maxim4ik163/ToneRealAdapter/Reference_PCB's/2 Mics_ An over-engineered solution – Exfil.co_files/IMG_7771.jpg

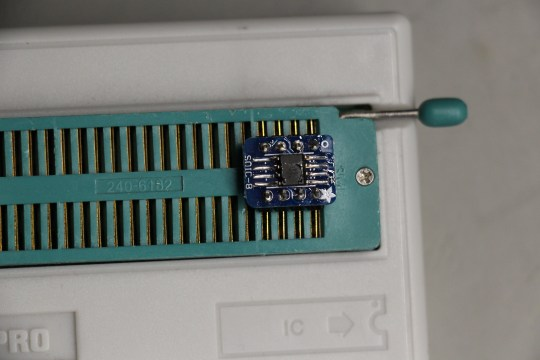
Reference_PCB's/2 Mics_ An over-engineered solution – Exfil.co_files/IMG_7771.jpg
