maxim4ik163/ToneRealAdapter/Reference_PCB's/2 Mics_ An over-engineered solution – Exfil.co_files/Screen-Shot-2018-05-16-11.10.27-AM.png

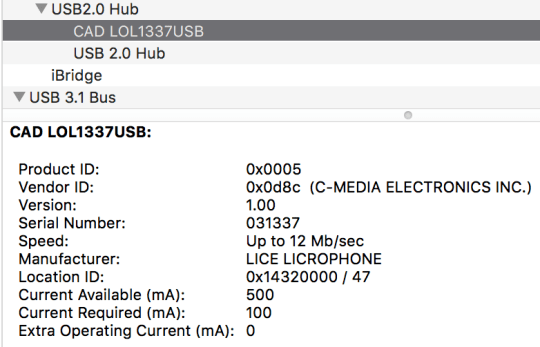
Reference_PCB's/2 Mics_ An over-engineered solution – Exfil.co_files/Screen-Shot-2018-05-16-11.10.27-AM.png
