maxim4ik163/ToneRealAdapter/Reference_PCB's/Bird UM-1_0.jpg

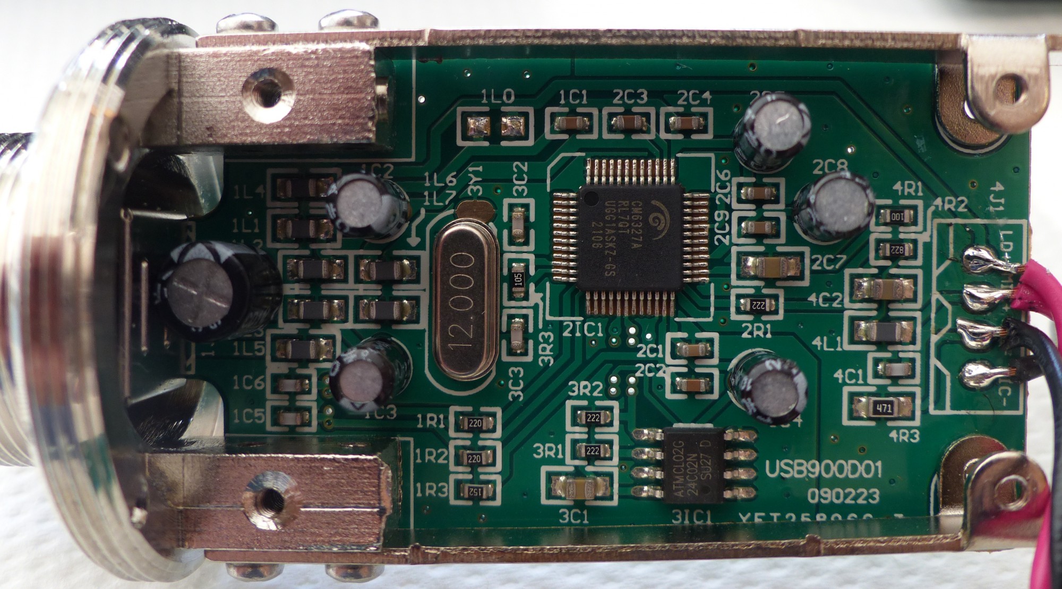
Reference_PCB's/Bird UM-1_0.jpg
