maxim4ik163/ToneRealAdapter/Reference_PCB's/blue_snowball_ice_1.0.jpg

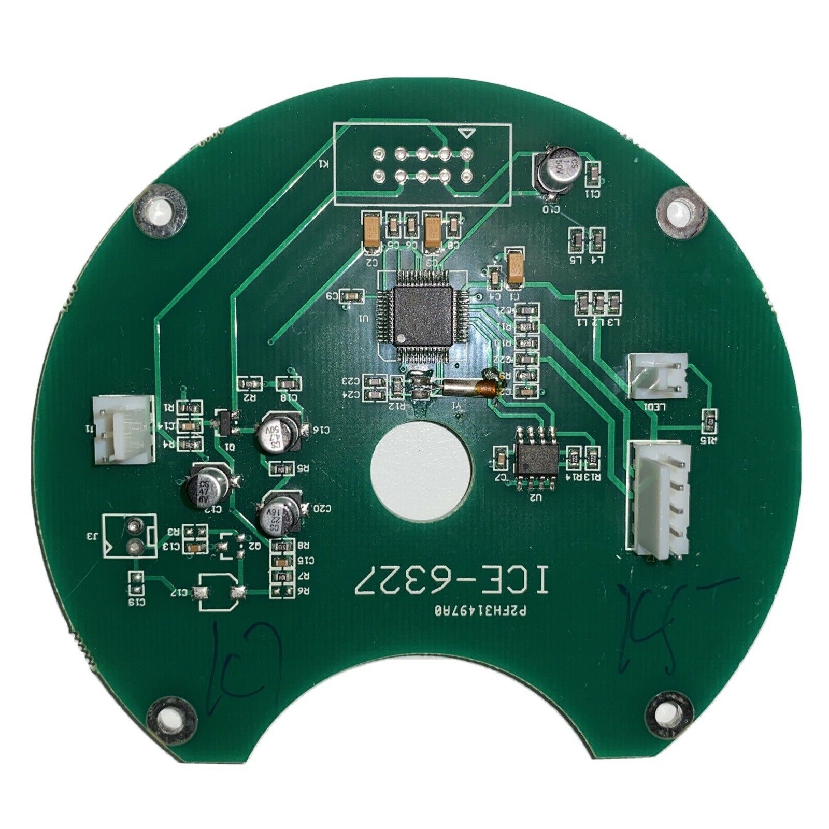
Reference_PCB's/blue_snowball_ice_1.0.jpg
