maxim4ik163/ToneRealAdapter/Reference_PCB's/blue_snowball_ice_1.1_back+mirror.png

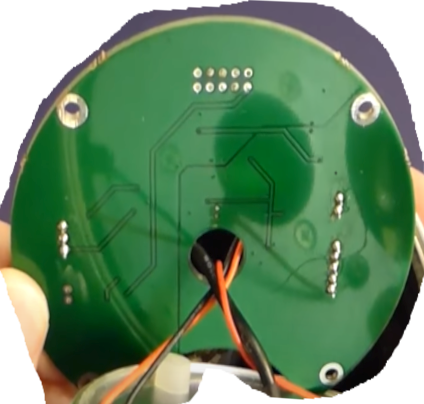
Reference_PCB's/blue_snowball_ice_1.1_back+mirror.png
