maxim4ik163/ToneRealAdapter/Reference_PCB's/blue_snowball_ice_1.2_back.png

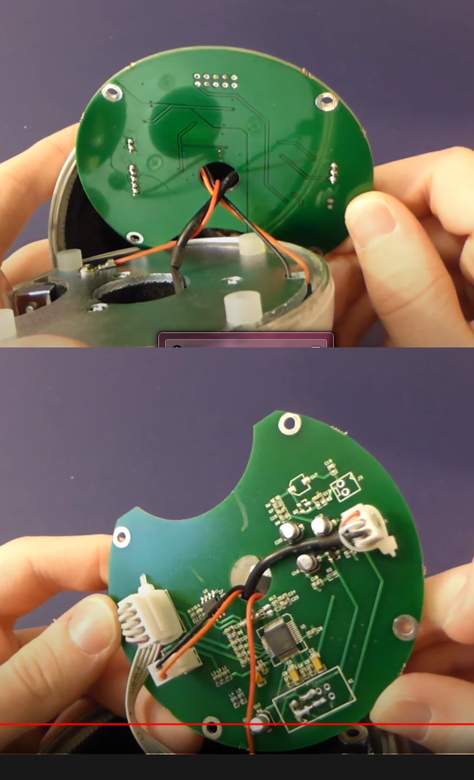
Reference_PCB's/blue_snowball_ice_1.2_back.png
