maxim4ik163/ToneRealAdapter/Reference_PCB's/blue_snowball_ice_1.3_back_mirror.png

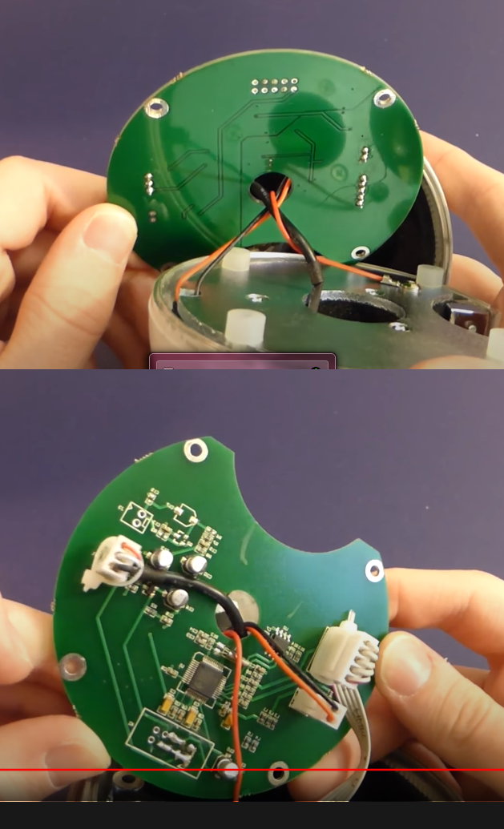
Reference_PCB's/blue_snowball_ice_1.3_back_mirror.png
