maxim4ik163/ToneRealAdapter/Reference_PCB's/blue_snowball_ice_1.4.png

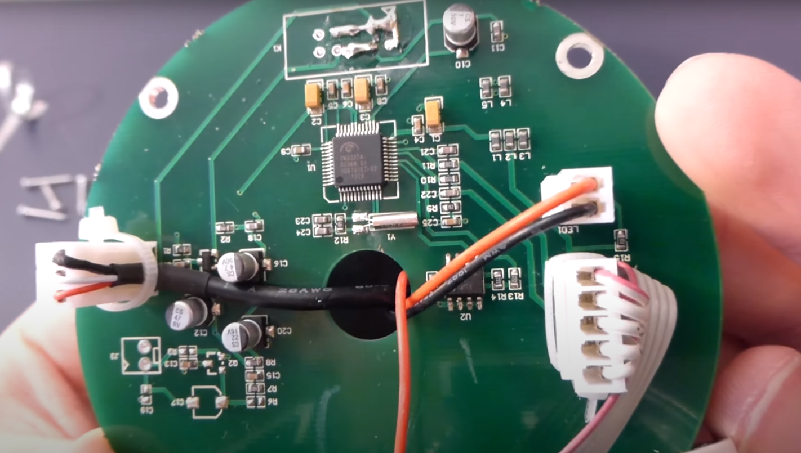
Reference_PCB's/blue_snowball_ice_1.4.png
