maxim4ik163/ToneRealAdapter/Reference_PCB's/DEXP_BK-20.png

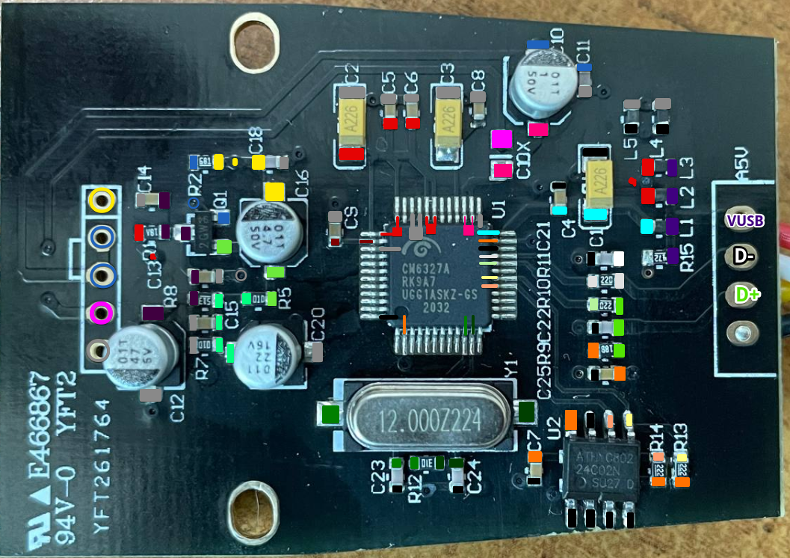
Reference_PCB's/DEXP_BK-20.png
