maxim4ik163/ToneRealAdapter/Reference_PCB's/dexp_etc_0.jpg

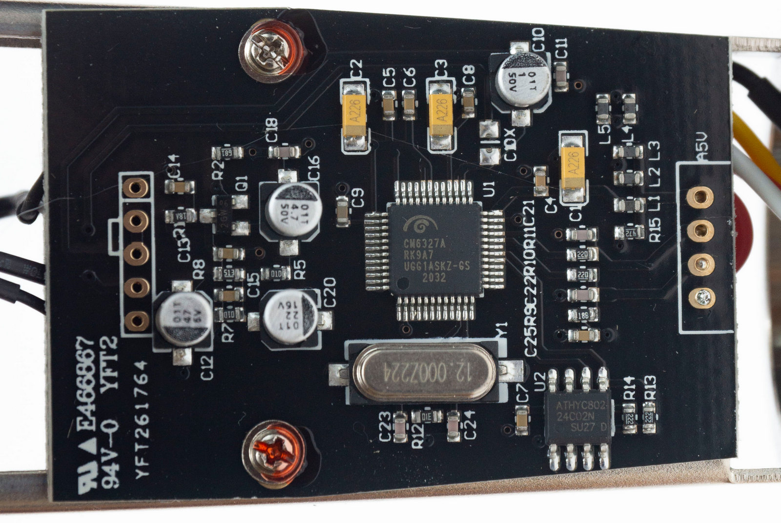
Reference_PCB's/dexp_etc_0.jpg
