maxim4ik163/ToneRealAdapter/Reference_PCB's/dexp_etc_1.jpg

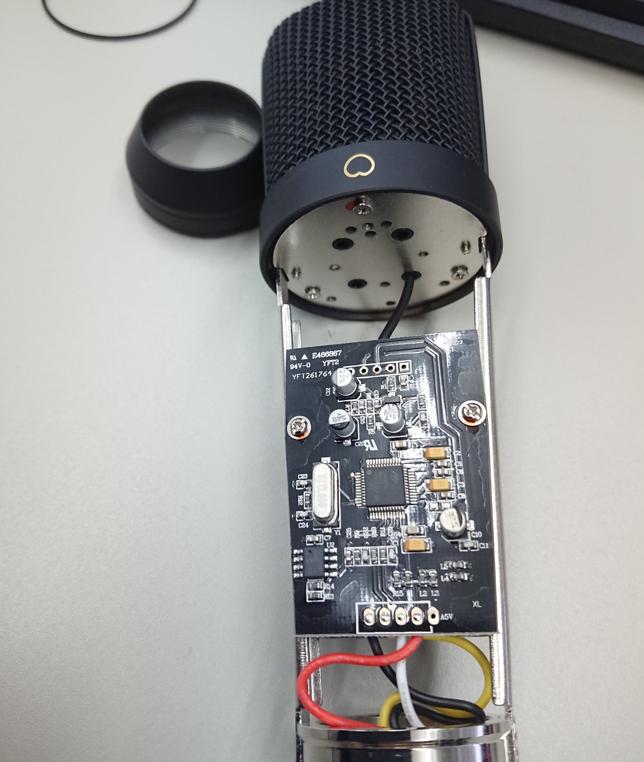
Reference_PCB's/dexp_etc_1.jpg
