maxim4ik163/ToneRealAdapter/Reference_PCB's/dexp_etc_2.jpeg

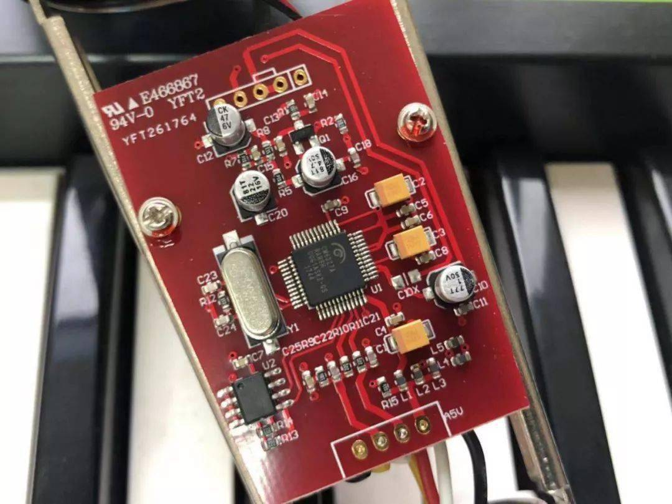
Reference_PCB's/dexp_etc_2.jpeg
