maxim4ik163/ToneRealAdapter/Reference_PCB's/RGA_1.jpg

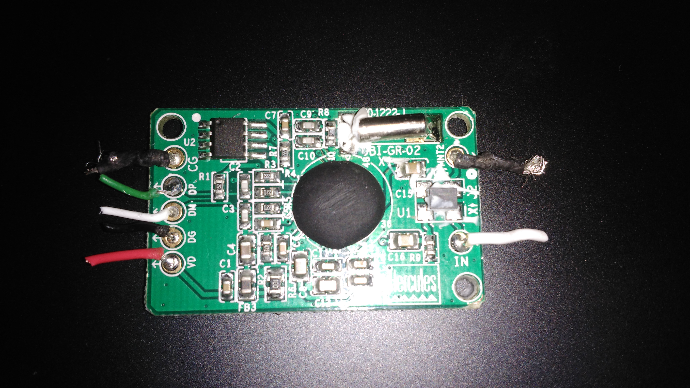
Reference_PCB's/RGA_1.jpg
