maxim4ik163/ToneRealAdapter/Reference_PCB's/trust-emita-16.webp

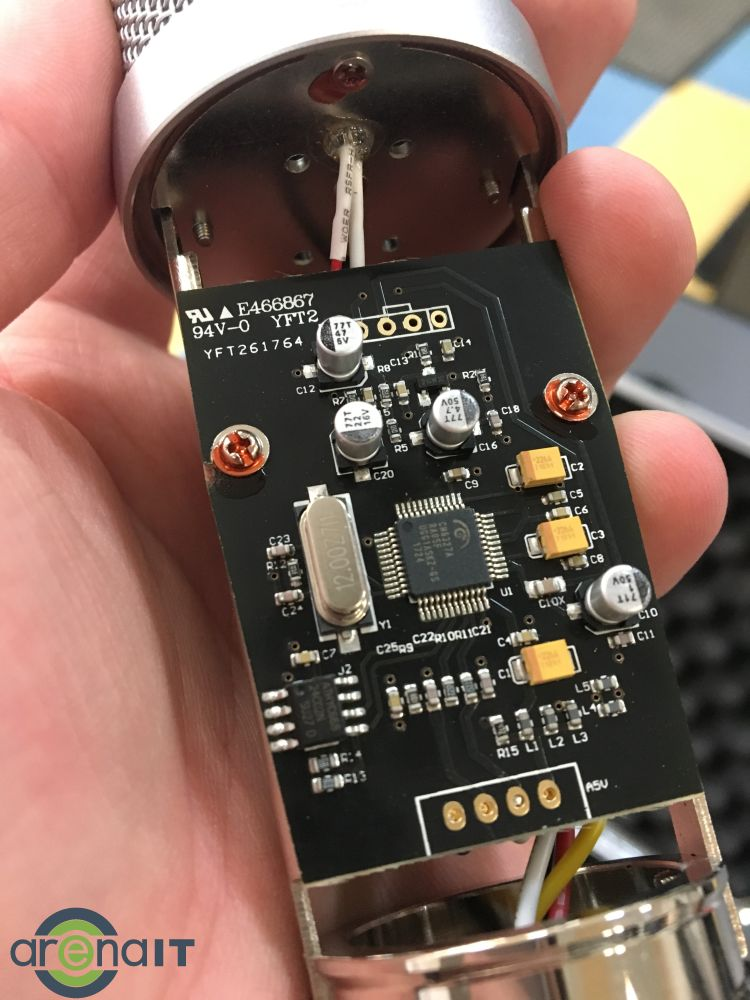
Reference_PCB's/trust-emita-16.webp
