maxim4ik163/ToneRealAdapter/Reference_PCB's/Trust_Buzz_1.jpg

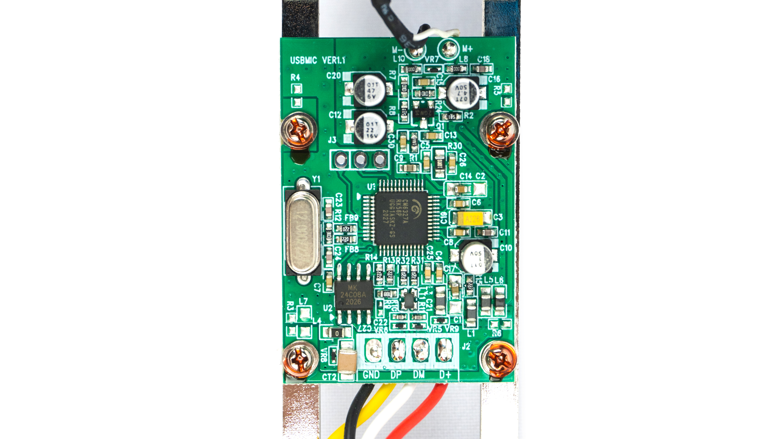
Reference_PCB's/Trust_Buzz_1.jpg
