maxim4ik163/ToneRealAdapter/Reference_PCB's/01_test_mikrofonu_genesis_radium_600_domowe_studio_nagran_nc1_b.jpg

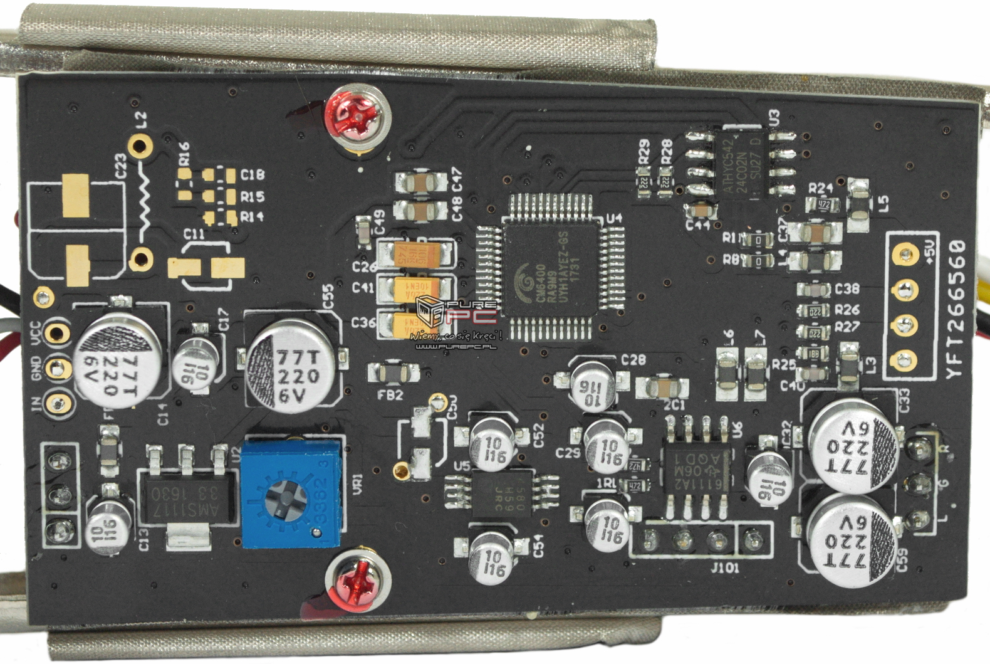
Reference_PCB's/01_test_mikrofonu_genesis_radium_600_domowe_studio_nagran_nc1_b.jpg
